borgel/sympetrum-v2/Hardware/FF1.1/gerbers-PDF/sympetrum-v2 FF1.1-F.Paste.pdf

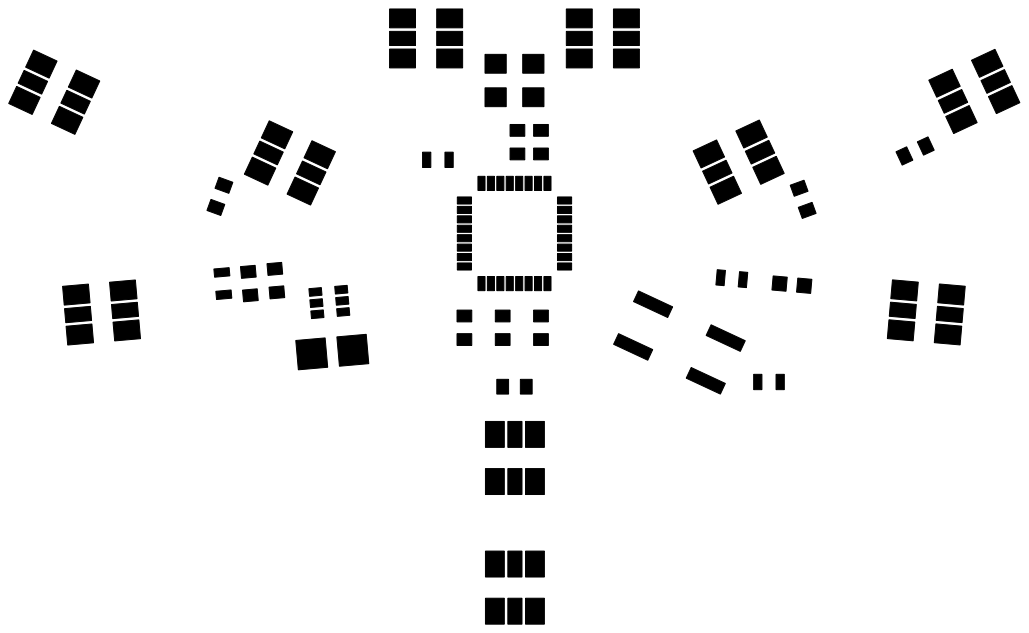
[picture p31: page 1]
