borgel/sympetrum-v2/Hardware/FF1.1/gerbers-PDF/sympetrum-v2 FF1.1-F.SilkS.pdf

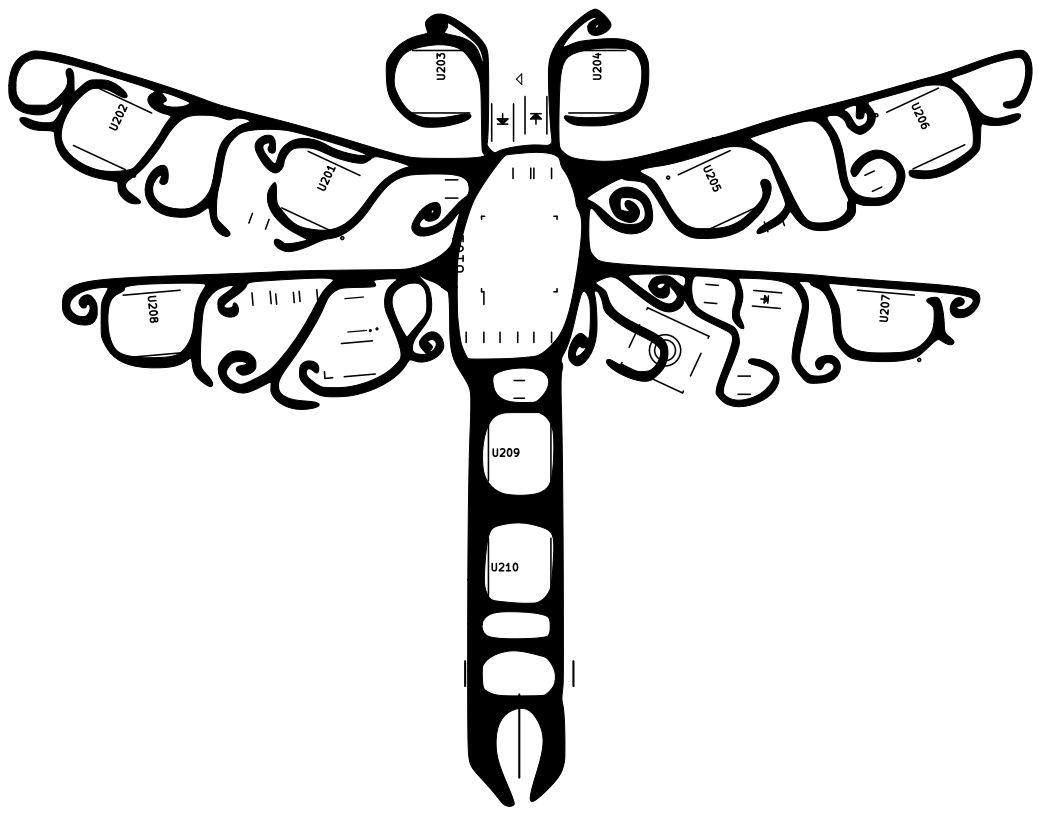
[picture p32: page 1]
