borgel/sympetrum-v2/Hardware/FF1.1/gerbers-PDF/sympetrum-v2 FF1.1-Top_Copper.pdf

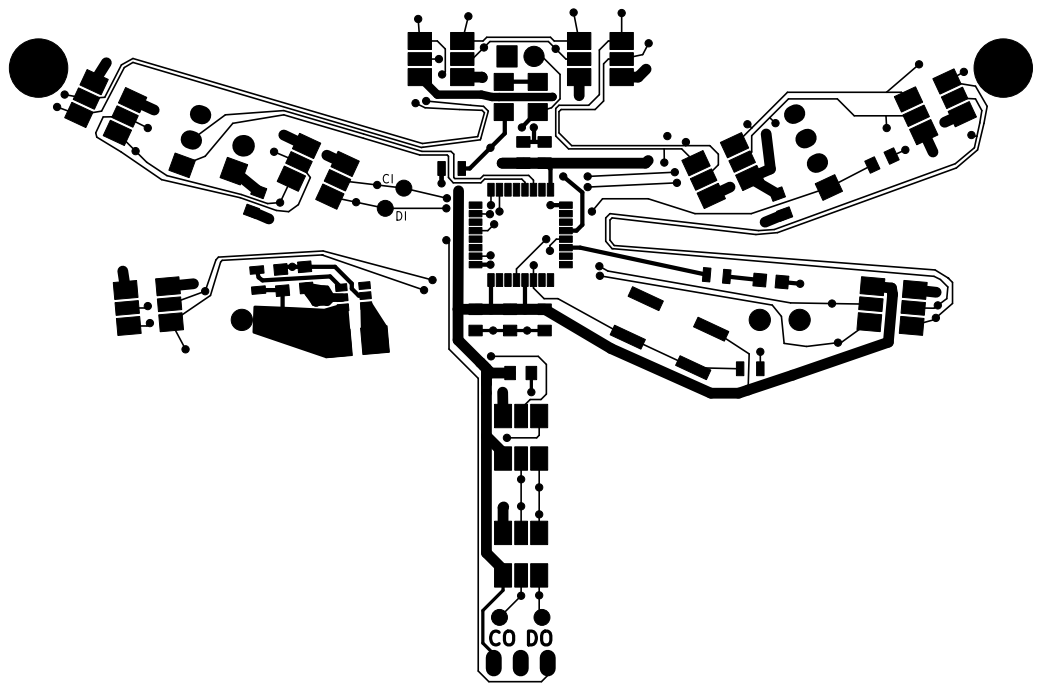
[picture p33: page 1]
