borgel/sympetrum-v2/Firmware/Inc/color.h

#ifndef COLOR_H__
#define COLOR_H__

/*
 * Generic colors and utilities. Derived from
 * https://github.com/borgel/sympetrum
 */

#include <stdint.h>

#pragma pack(push)  /* push current alignment to stack */
#pragma pack(1)     /* set alignment to 1 byte boundary */
struct color_ColorRGB {
   uint8_t     b;
   uint8_t     g;
   uint8_t     r;
};
#pragma pack(pop)   /* restore original alignment from stack */

#define HSV_CHANNEL_MAX          255
#define HSV_CHANNEL_MIN          0

//TODO check these
#define HSV_COLOR_R              0
#define HSV_COLOR_G              127
#define HSV_COLOR_B              254

struct color_ColorHSV {
   uint8_t     h;
   uint8_t     s;
   uint8_t     v;
};

//AKA white
static const struct color_ColorHSV COLOR_HSV_WHITE = {
   .h = 0,
   .s = 0,
   .v = HSV_CHANNEL_MAX
};

//AKA black
static const struct color_ColorHSV COLOR_HSV_BLACK = {
   .h = 0,
   .s = 0,
   .v = HSV_CHANNEL_MIN
};

void color_HSV2RGB(struct color_ColorHSV const *hsv, struct color_ColorRGB *rgb);

#endif//COLOR_H__
