borgel/sympetrum-v2/Firmware/Inc/iprintf.h

/******************************************************************************
*This file is for iprintf()
*******************************************************************************/
#ifndef IPRINTF_H
#define IPRINTF_H

void iprintf(char *pszFmt,...);

#endif
/* [] END OF FILE */
