borgel/sympetrum-v2/Firmware/Inc/utilities.h

#ifndef UTILITIES_H__
#define UTILITIES_H__

#define MAX(a,b) \
   ({ __typeof__ (a) _a = (a); \
    __typeof__ (b) _b = (b); \
    _a > _b ? _a : _b; })

#define MIN(a,b) \
   ({ __typeof__ (a) _a = (a); \
    __typeof__ (b) _b = (b); \
    _a > _b ? _b : _a; })

#endif//UTILITIES_H__
